evanman83/OURS-project/photos/IMG_1463.JPG

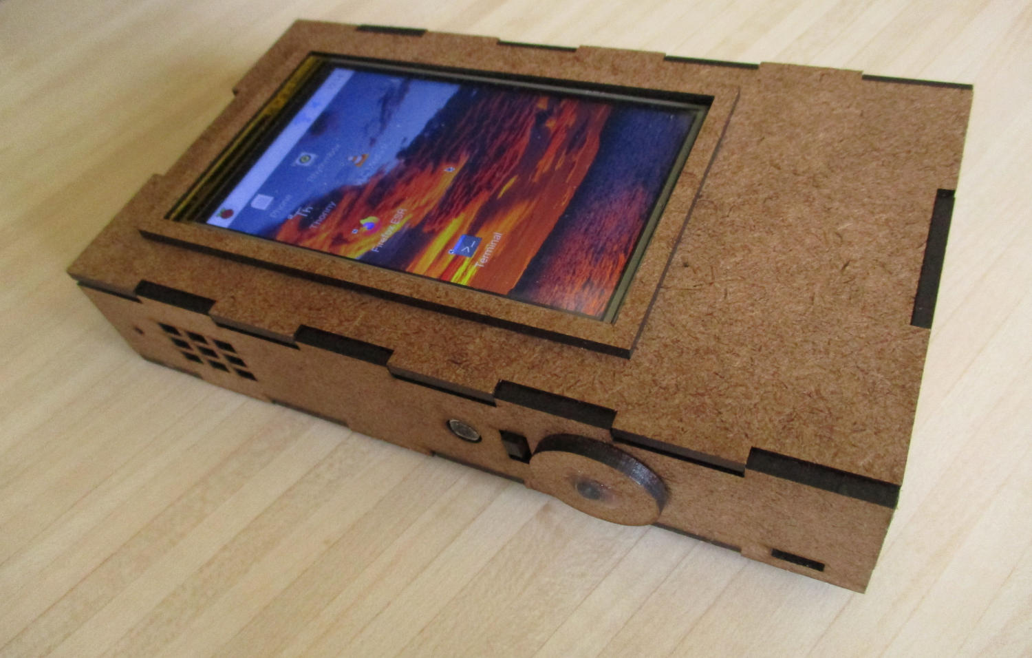
photos/IMG_1463.JPG
