evanman83/OURS-project/photos/IMG_20230429_135159.jpg

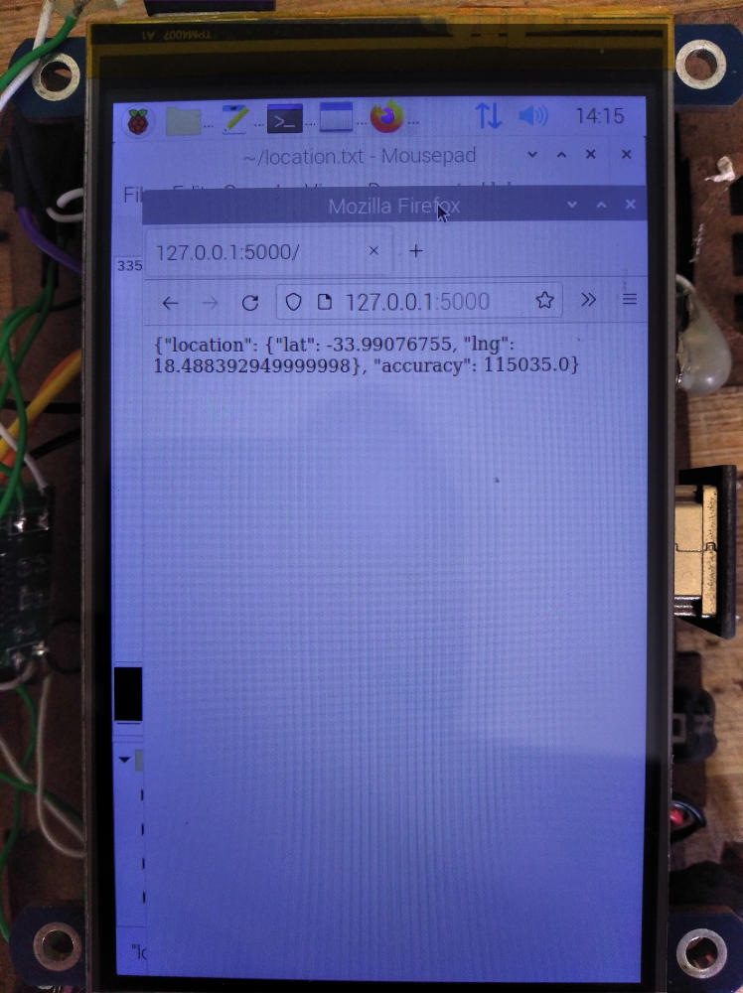
photos/IMG_20230429_135159.jpg
