evanman83/OURS-project/photos/IMG_20230430_202821.jpg

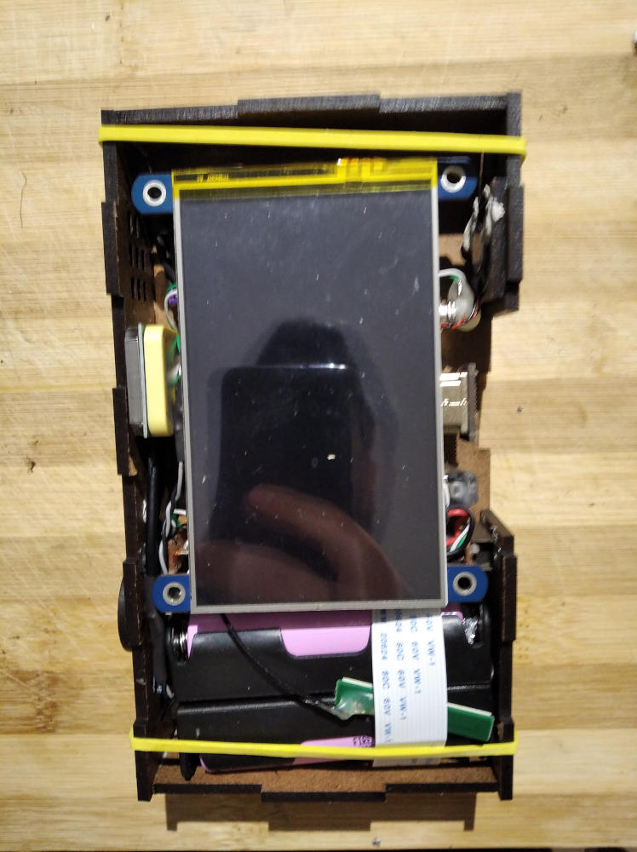
photos/IMG_20230430_202821.jpg
