evanman83/OURS-project/photos/IMG_20230501_112252.jpg

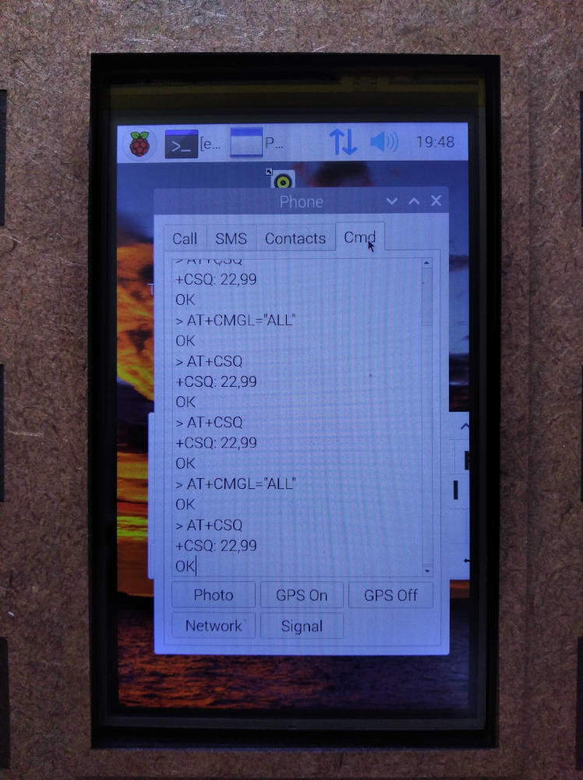
photos/IMG_20230501_112252.jpg
