evanman83/OURS-project/photos/IMG_20230501_113514.jpg

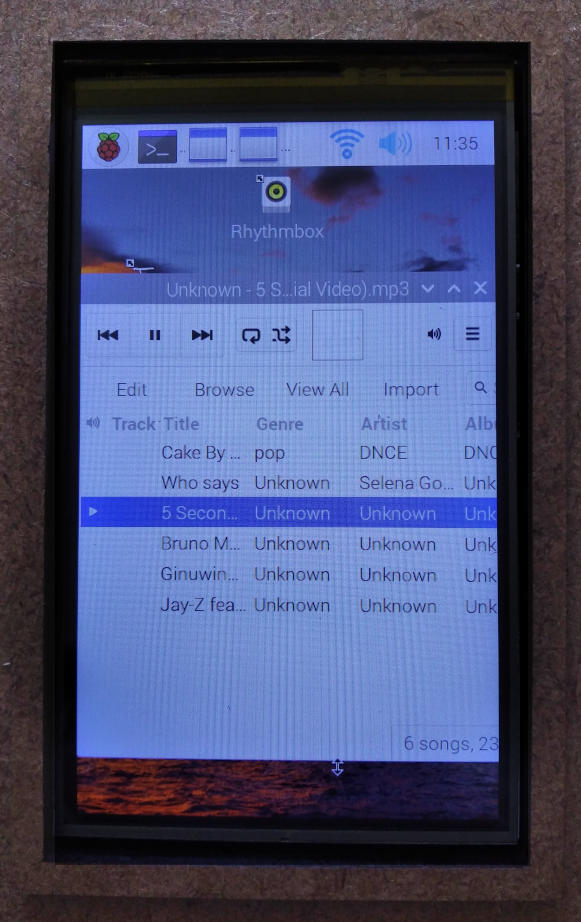
photos/IMG_20230501_113514.jpg
