evanman83/OURS-project/photos/IMG_20230501_115911.jpg

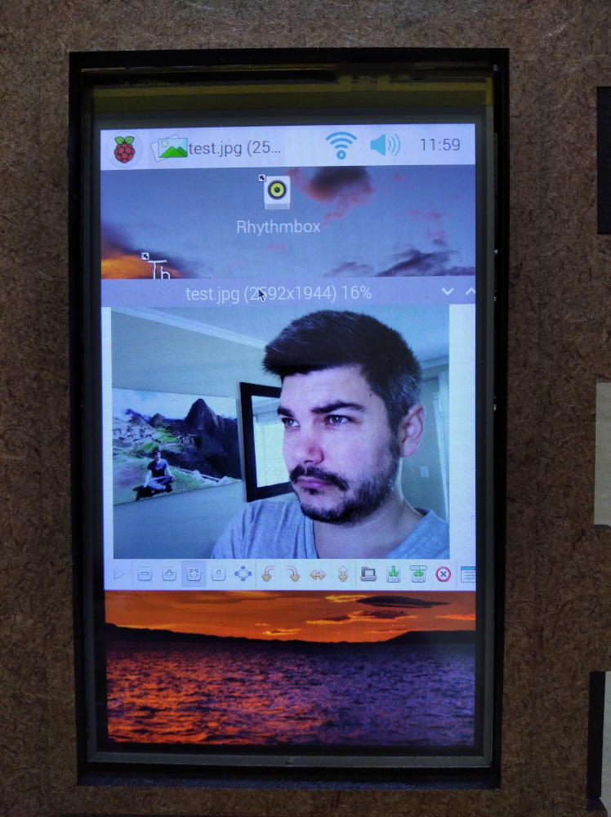
photos/IMG_20230501_115911.jpg
